dkorschu/DiKo_PreAmp/Version 2/Notebook/img/Hochpass.png

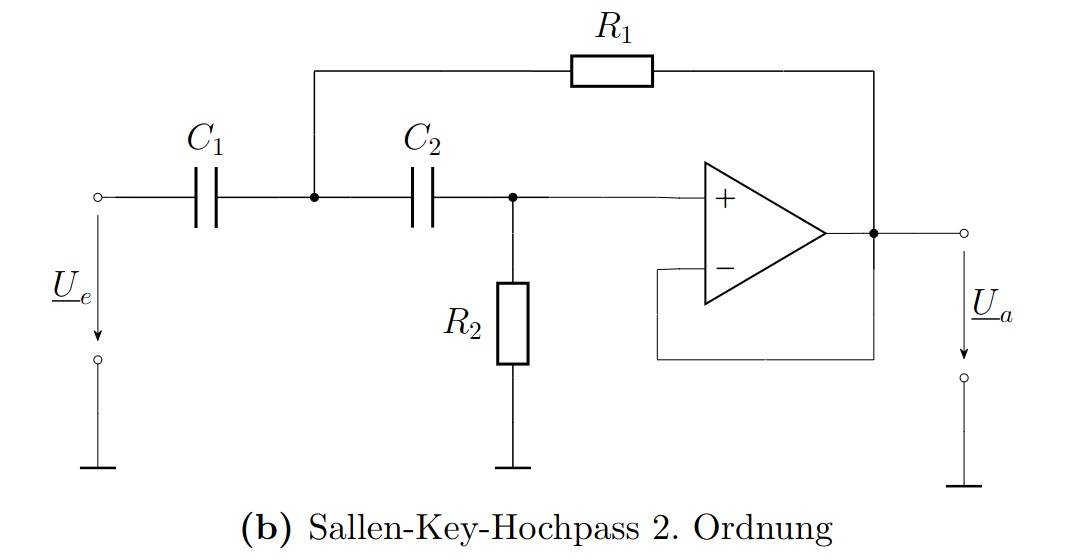
Version 2/Notebook/img/Hochpass.png
