dkorschu/DiKo_PreAmp/Version 2/Pictures/1dBu.jpg

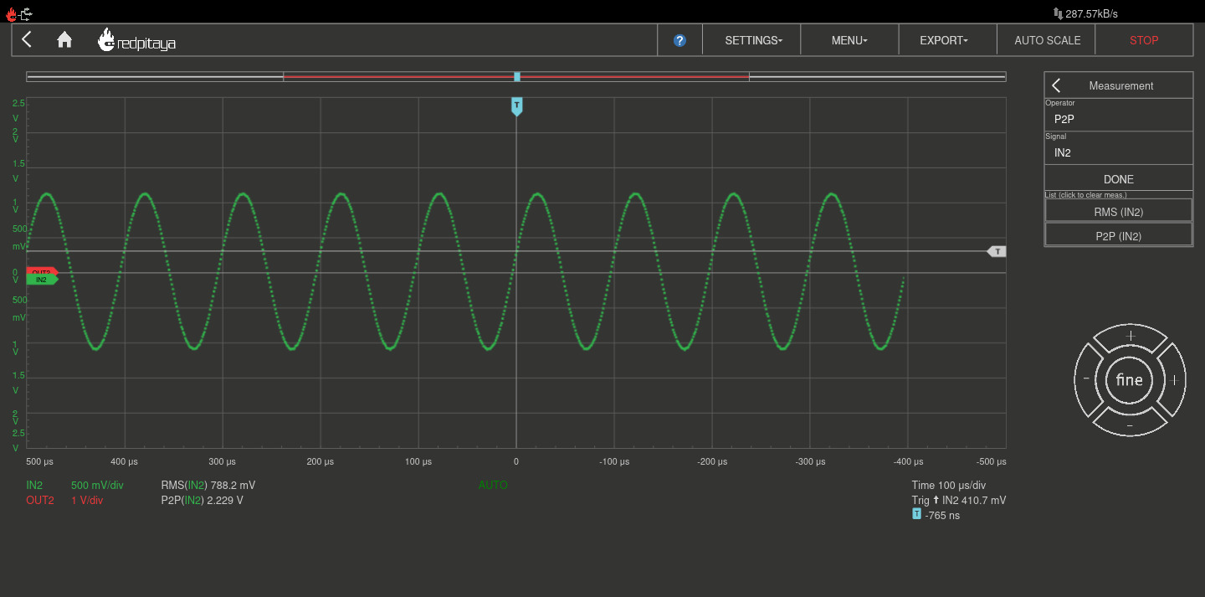
Version 2/Pictures/1dBu.jpg
