dkorschu/DiKo_PreAmp/Version 2/Pictures/Höhen_Bandpass_Bode.jpg

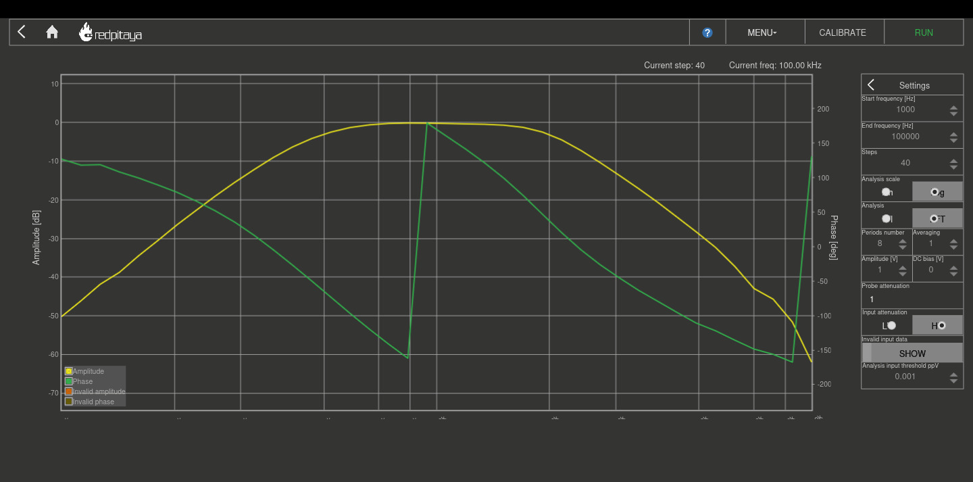
Version 2/Pictures/Höhen_Bandpass_Bode.jpg
