dkorschu/DiKo_PreAmp/Version 2/Pictures/Impression_Eingangsstufe_1.jpg

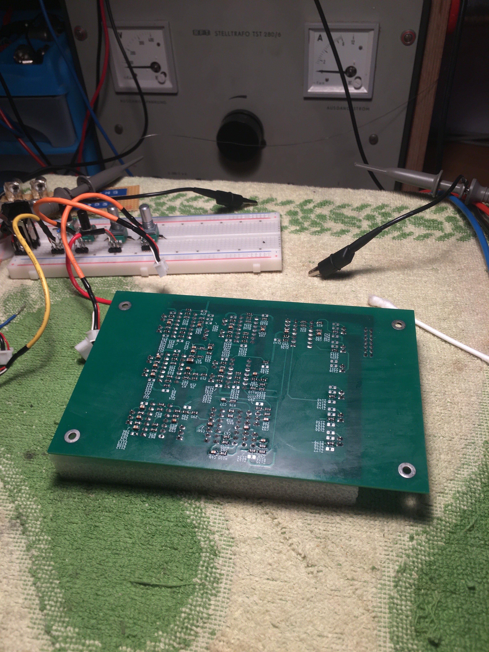
Version 2/Pictures/Impression_Eingangsstufe_1.jpg
