dkorschu/DiKo_PreAmp/Version 2/Pictures/Mitten_Bandpass_Bode.jpg

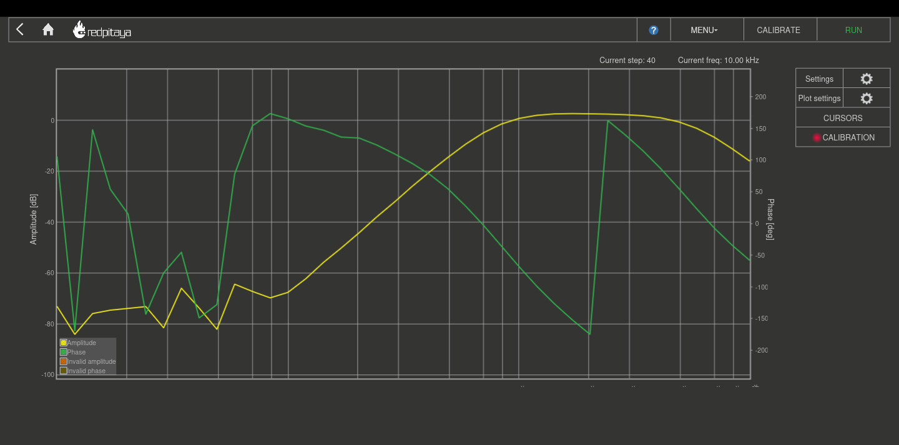
Version 2/Pictures/Mitten_Bandpass_Bode.jpg
