dkorschu/DiKo_PreAmp/Version 2/Pictures/Pre_Amp_Top_alt.jpg

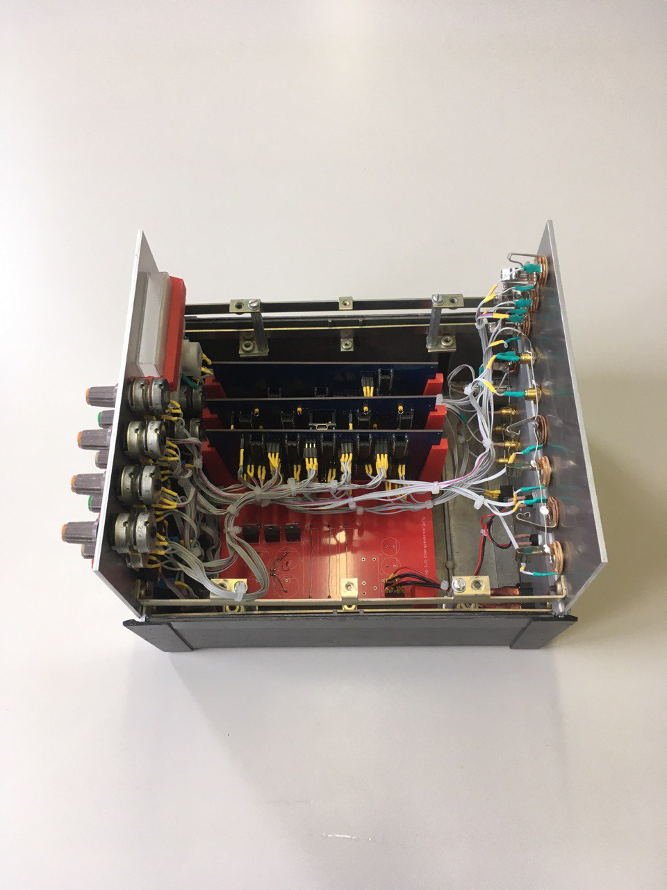
Version 2/Pictures/Pre_Amp_Top_alt.jpg
