dkorschu/DiKo_PreAmp/Version 2/Pictures/Sub_Bandpass_Bode.jpg

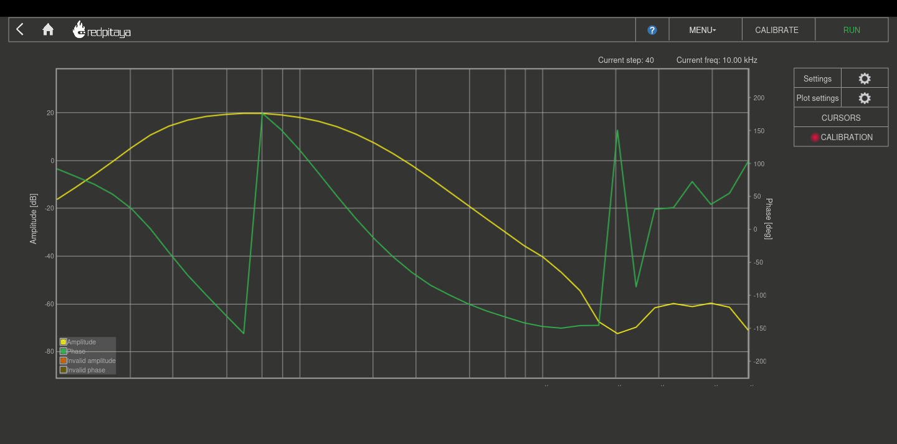
Version 2/Pictures/Sub_Bandpass_Bode.jpg
