dkorschu/DiKo_PreAmp/Version 2/Pictures/Whiteboard.jpg

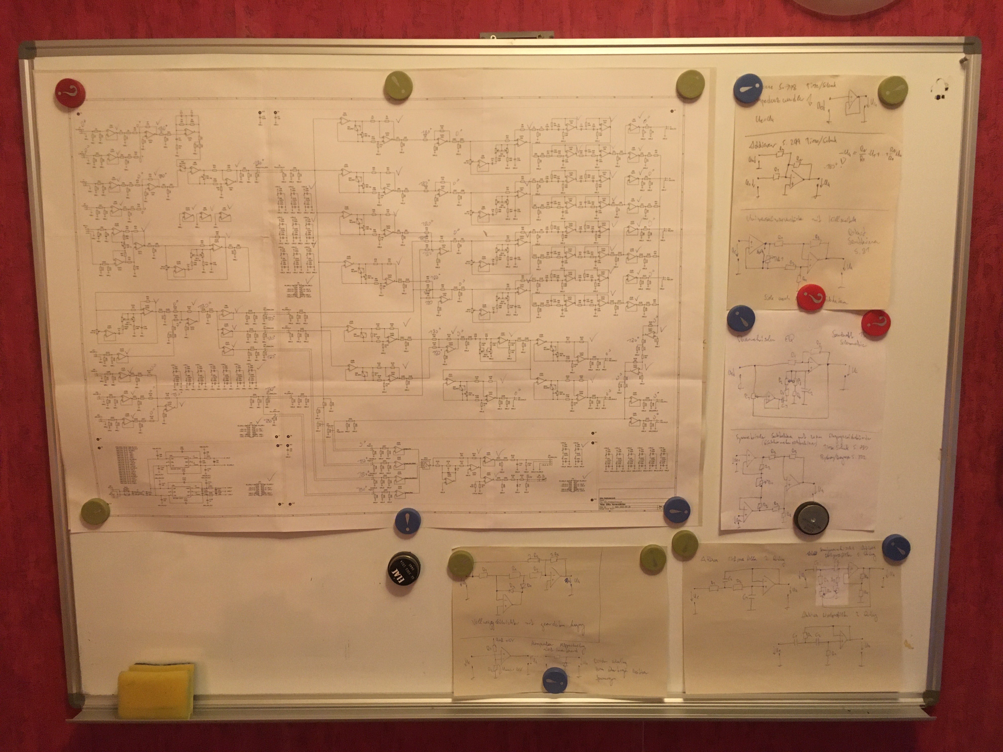
Version 2/Pictures/Whiteboard.jpg
