dkorschu/DiKo_PreAmp/Version 2/Pictures/VU_Test.jpg

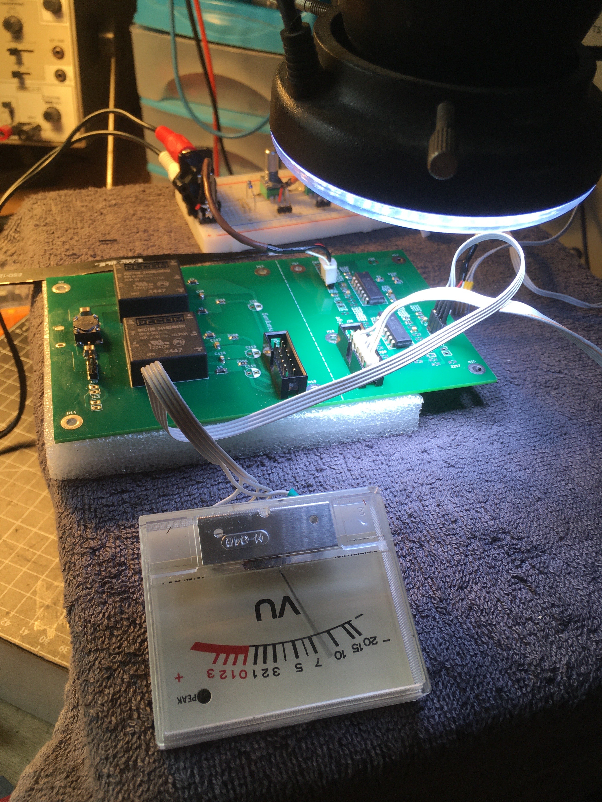
Version 2/Pictures/VU_Test.jpg
