dkorschu/DiKo_PreAmp/Version 2/Version 1/Altium/Energieversorgung/Project Outputs for Energieversorgung/Energieversorgung_alt.PDF

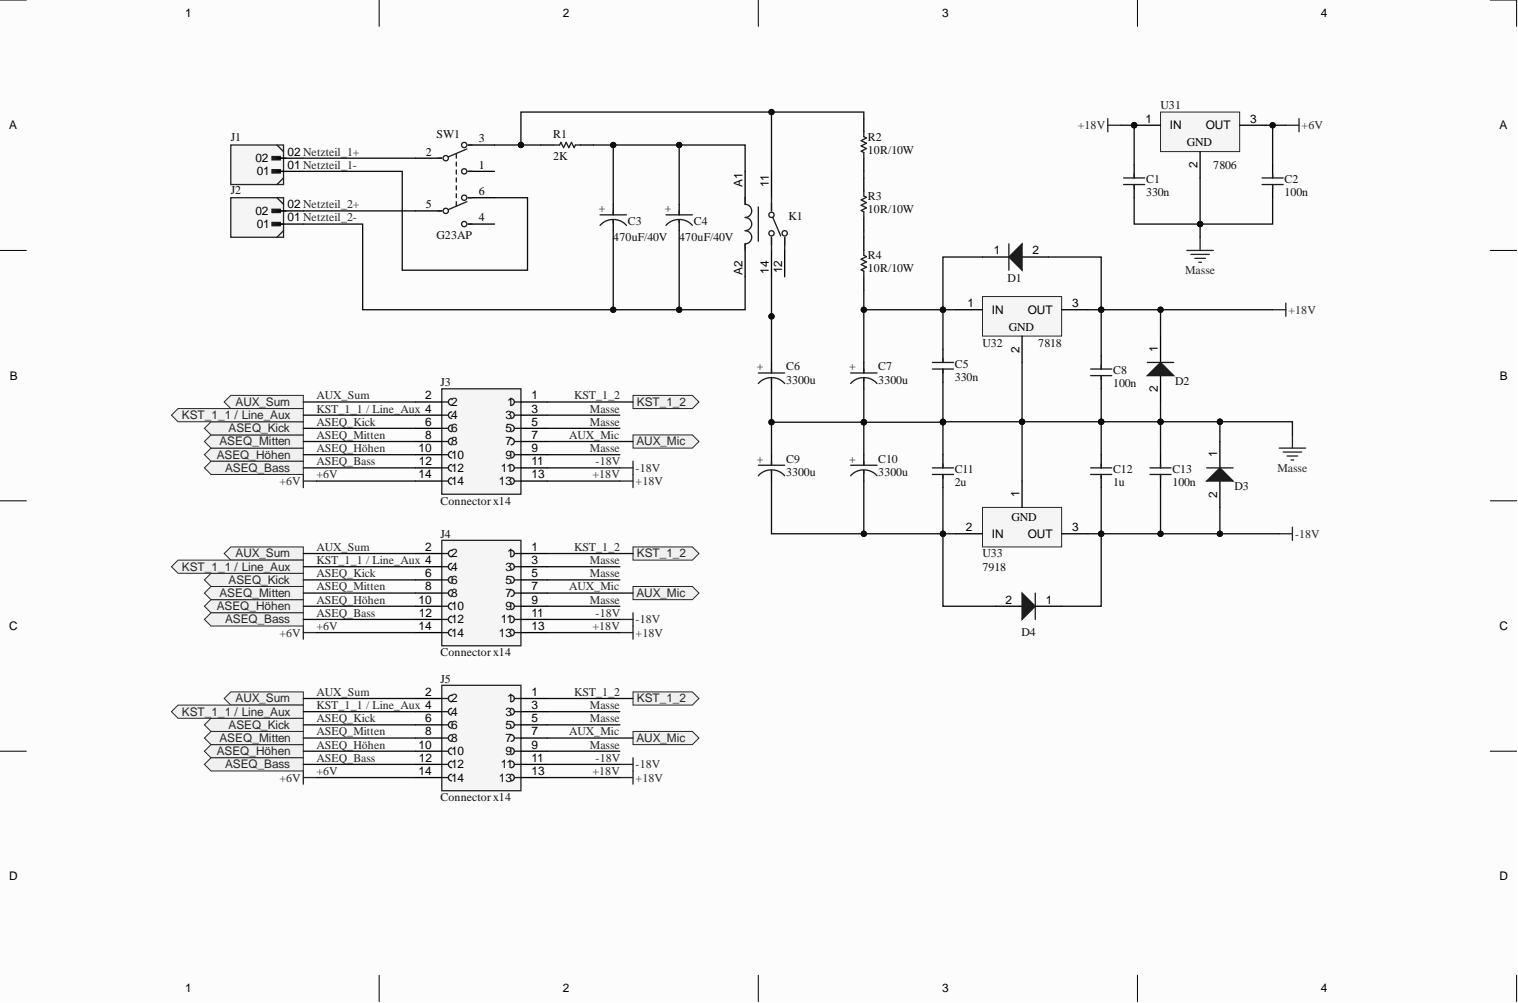
[picture p26: page 1]
