dkorschu/DiKo_PreAmp/Version 2/Version 1/Altium/Frequenzweiche/Project Outputs for Frequenzweiche/Job1.PDF

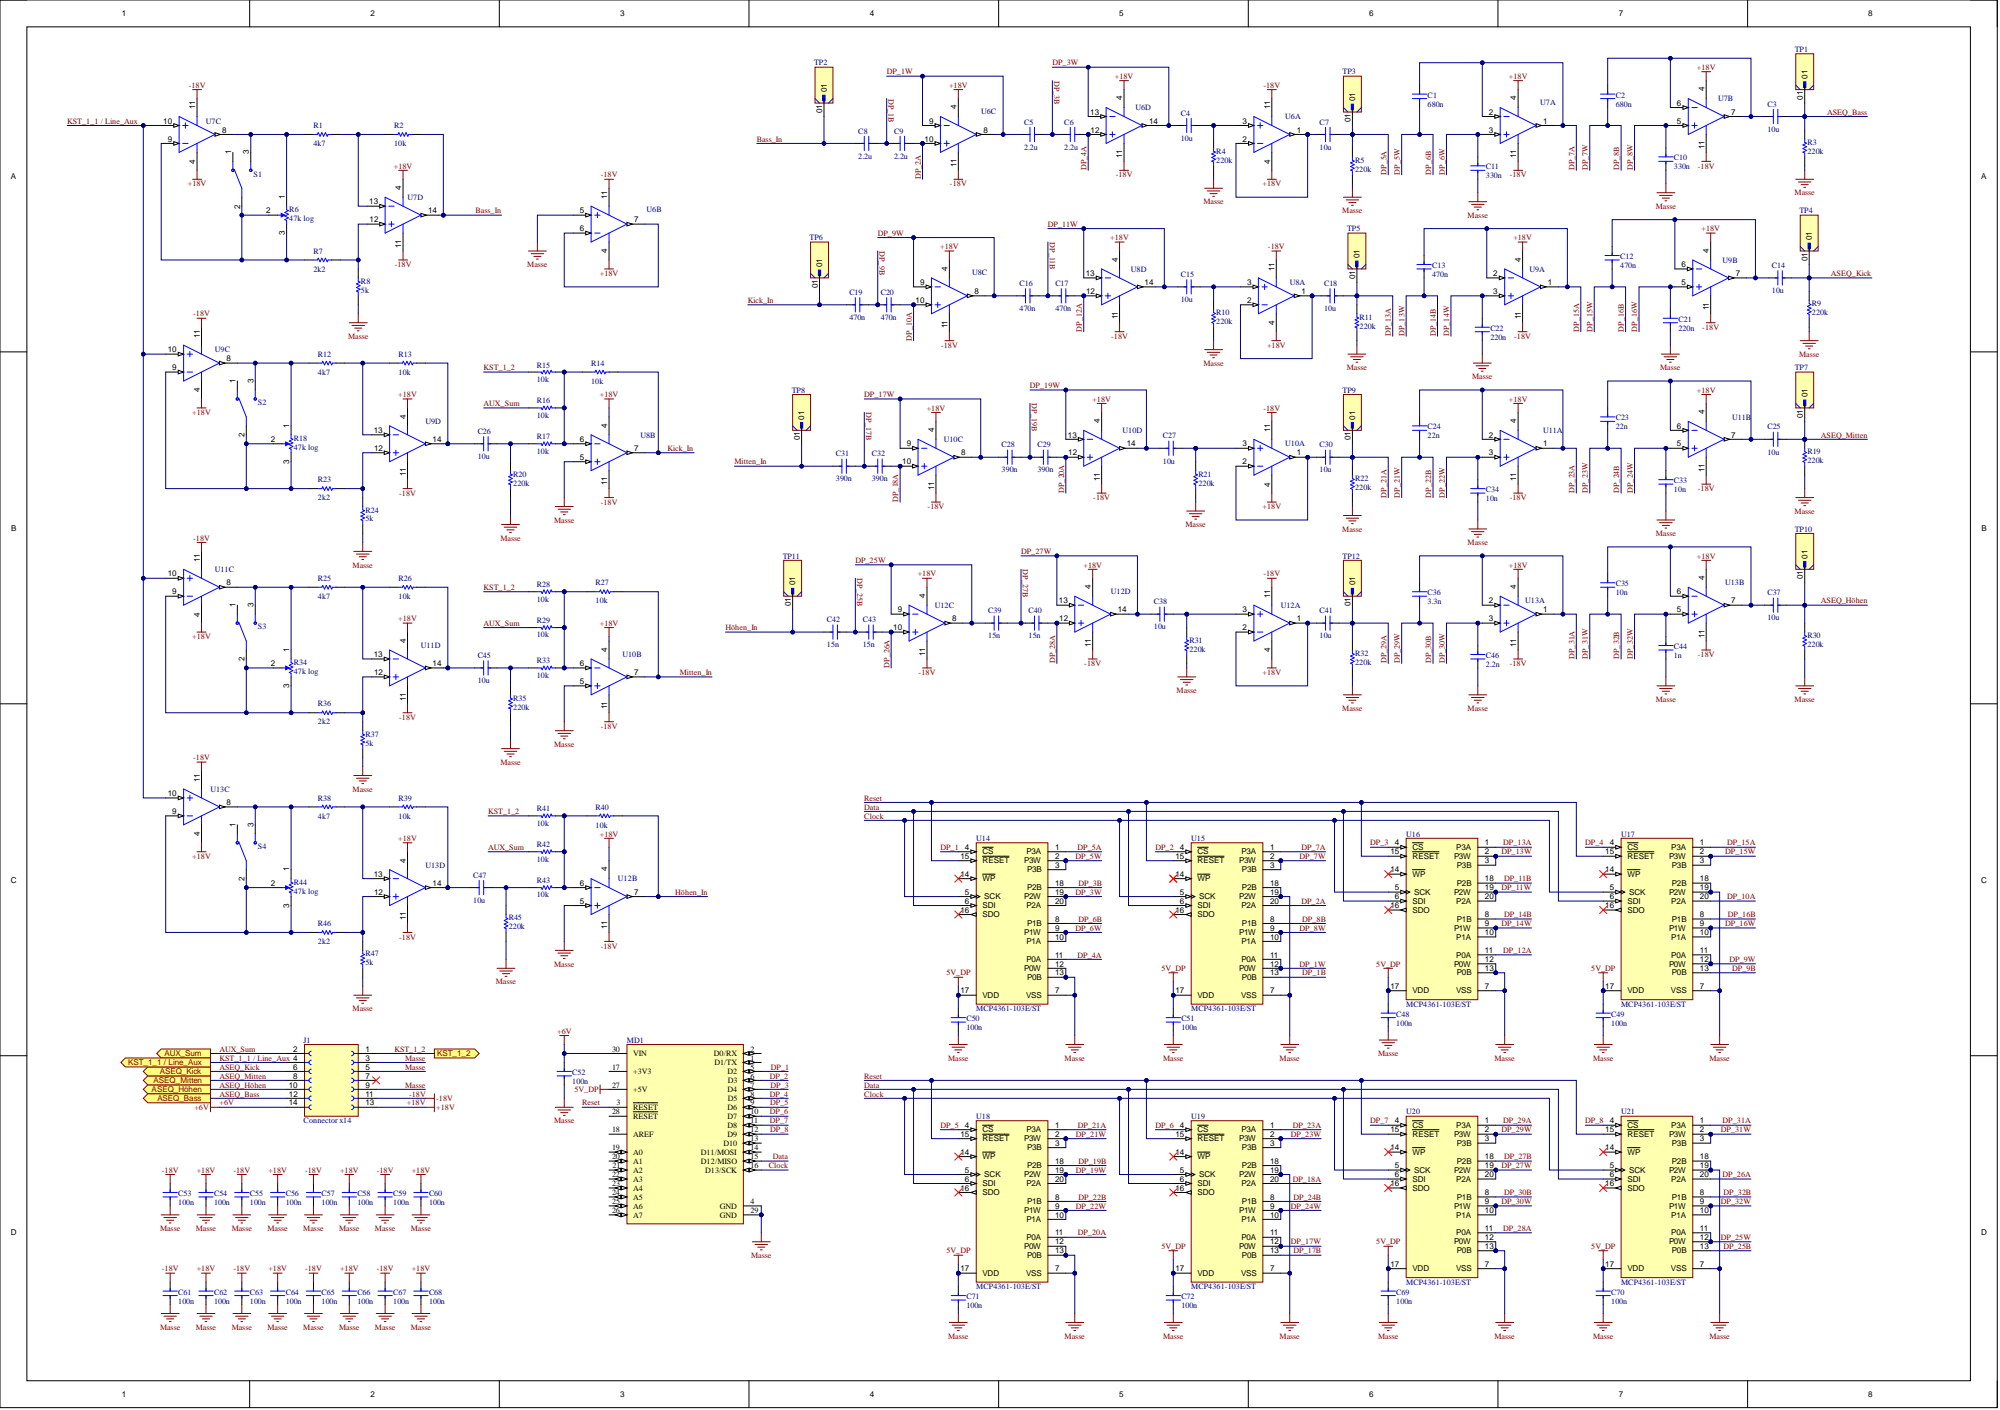
[picture p27: page 1]

Data
Clock

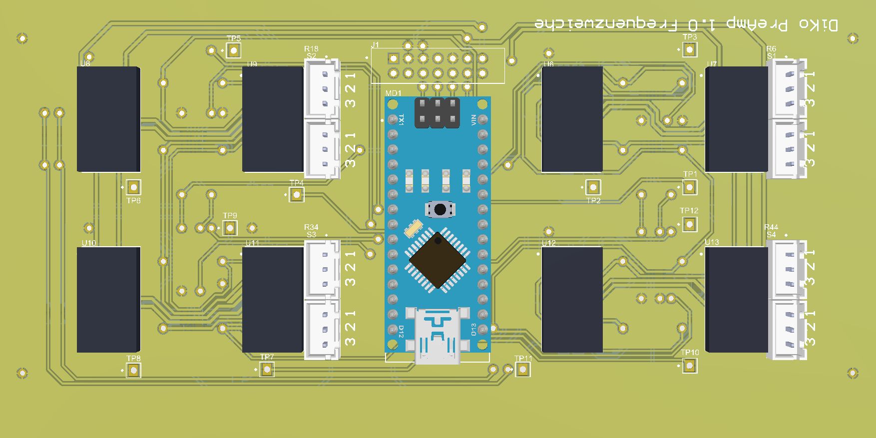
[picture p28: page 2]

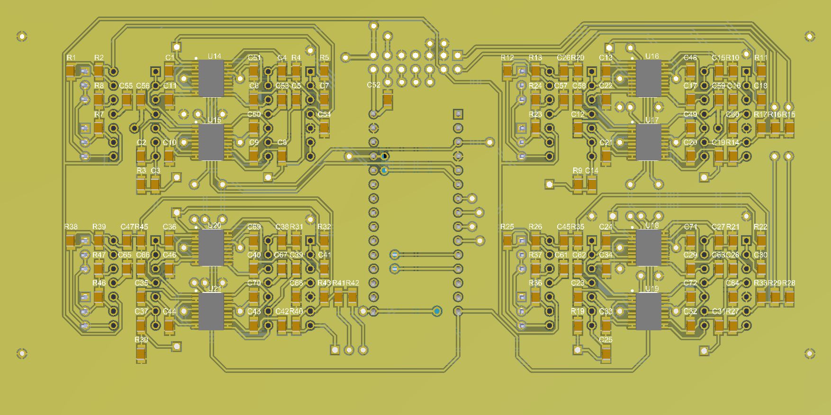
[picture p29: page 3]

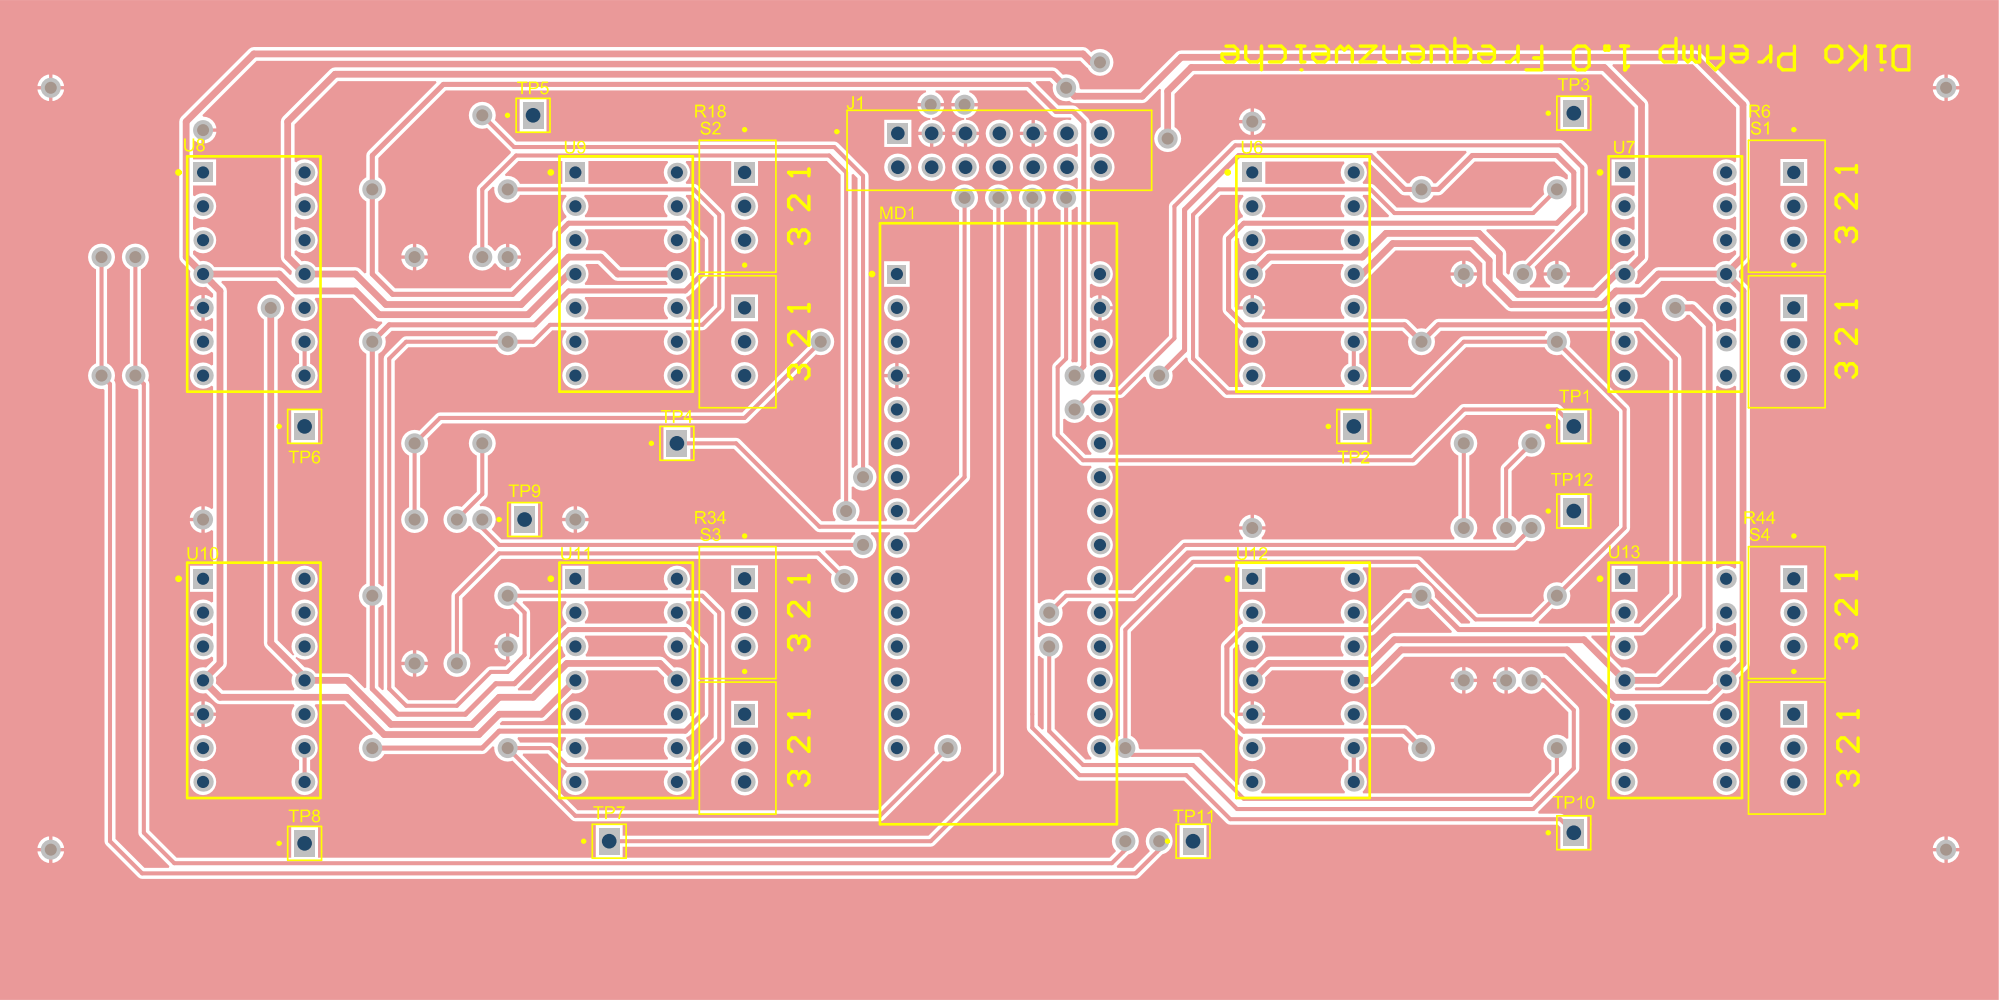
[picture p30: page 4]

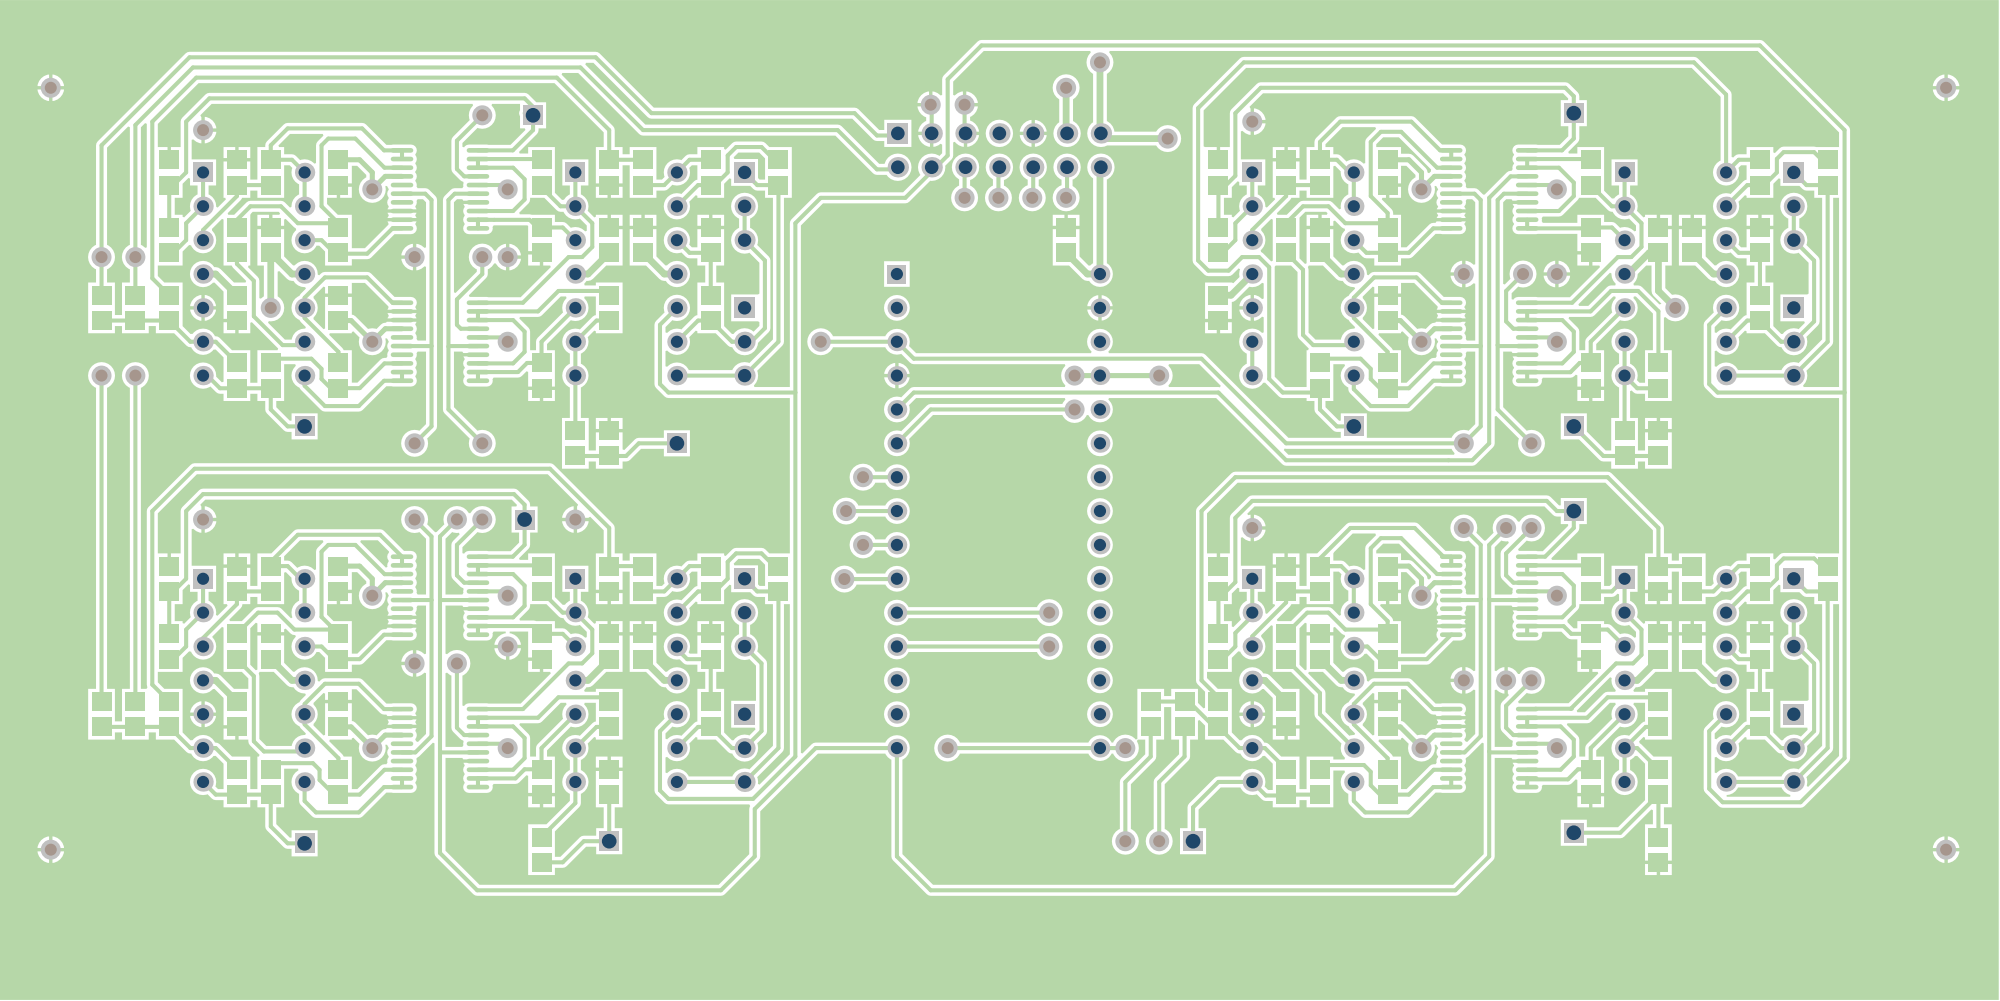
[picture p31: page 5]
